y0ukn0wwh0/ConsoleGame/Console/console box/box model.PNG

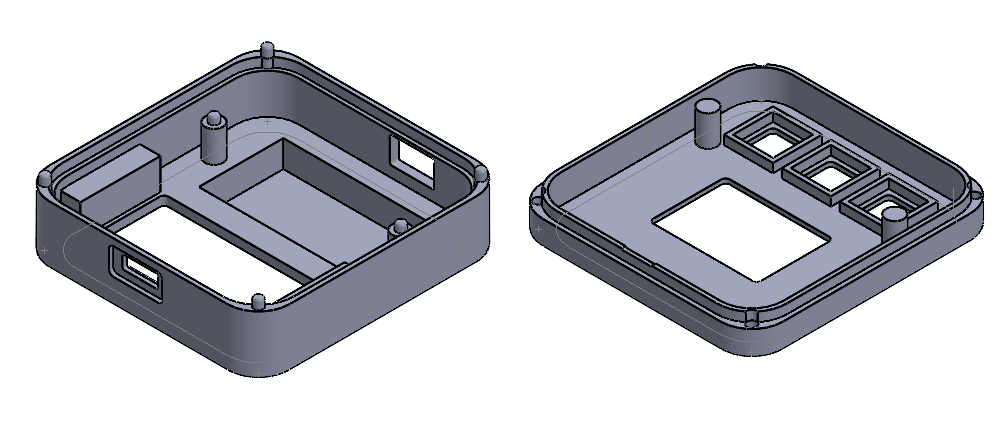
Console/console box/box model.PNG
