y0ukn0wwh0/ConsoleGame/Console/pcb.png

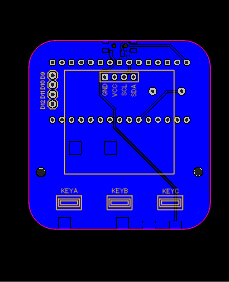
Console/pcb.png
