y0ukn0wwh0/ConsoleGame/images/feed.gif

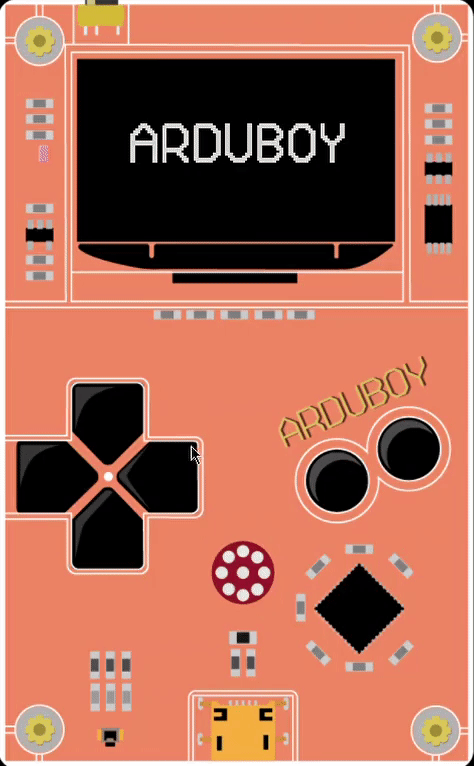
images/feed.gif
