y0ukn0wwh0/ConsoleGame/Showcase/box2.jpg

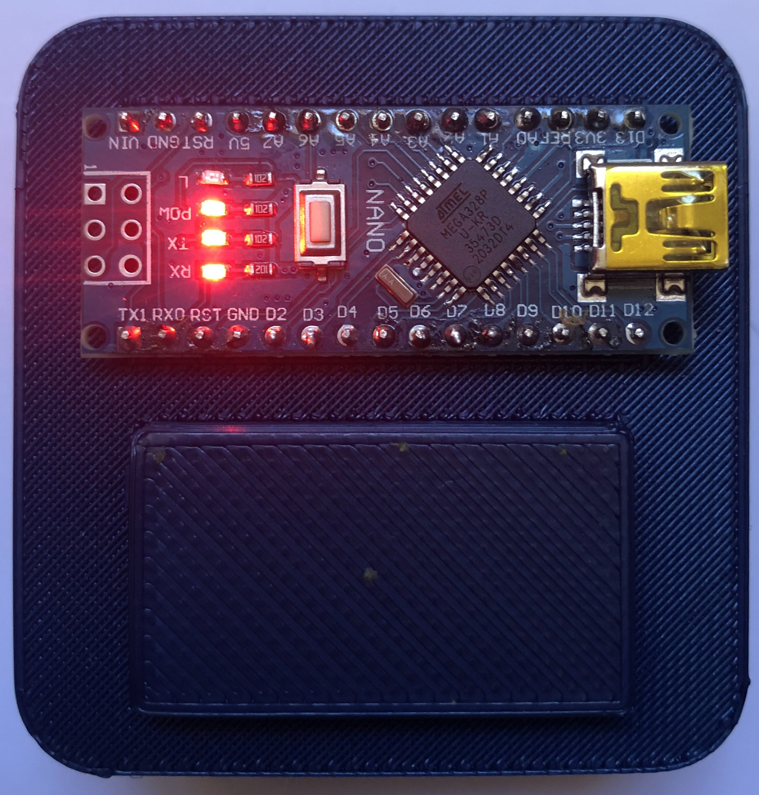
Showcase/box2.jpg
