y0ukn0wwh0/ConsoleGame/Showcase/box3.jpg

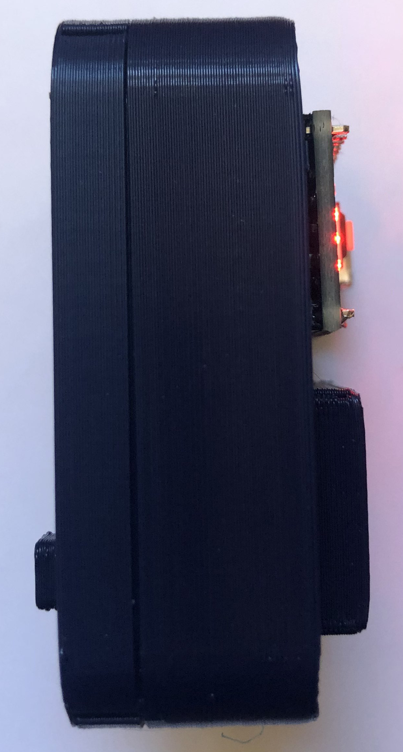
Showcase/box3.jpg
