y0ukn0wwh0/ConsoleGame/images/testComponents.gif

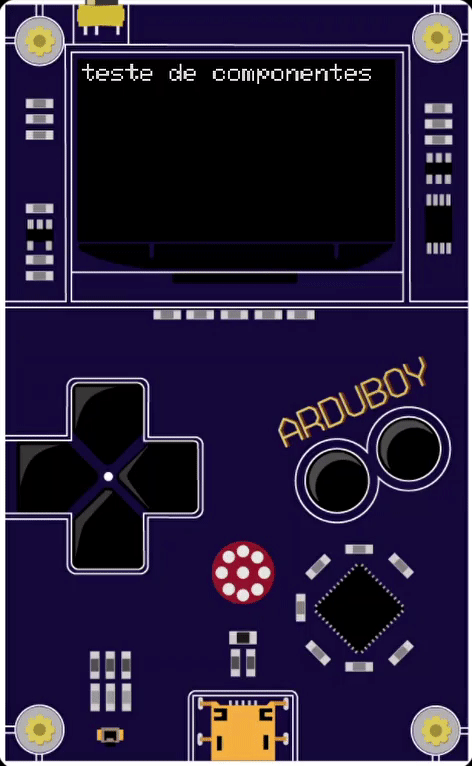
images/testComponents.gif
