y0ukn0wwh0/ConsoleGame/Game/game/sprites.c

#include <avr/pgmspace.h>

#ifndef SPRITES
#define SPRITES

//Game logo (73, 17)
const uint8_t PROGMEM logo[] = {
0x00, 0x00, 0xfc, 0xfc, 0xfc, 0xfc, 0xfc, 0x1c, 0x1c, 0x1c, 0xfc, 0xfc, 0xfc, 0xfc, 0xf8, 0x00, 0x00, 0x00, 0xfc, 0xfc, 0xfc, 0xfc, 0xfc, 0x00, 0x00, 0x00, 0xfc, 0xfc, 0xfc, 0xfc, 0xfc, 0x00, 0x00, 0x00, 0xfc, 0xfc, 0xfc, 0xfc, 0xfc, 0x1c, 0x1c, 0x1c, 0xfc, 0xfc, 0xfc, 0xfc, 0xf8, 0x00, 0x00, 0x00, 0xf8, 0xfc, 0xfc, 0xfc, 0xfc, 0x1c, 0x1c, 0x9c, 0x9c, 0x9c, 0x9c, 0x9c, 0x9c, 0x00, 0x00, 0x00, 0xfc, 0xfc, 0xfc, 0xfc, 0xfc, 0x00, 0x00, 
0x00, 0x00, 0x7f, 0x7f, 0x7f, 0x7f, 0x7f, 0x70, 0x70, 0x70, 0x7f, 0x7f, 0x7f, 0x7f, 0x3f, 0x00, 0x00, 0x00, 0x3f, 0x7f, 0x7f, 0x7f, 0x7f, 0x70, 0x70, 0x70, 0x7f, 0x7f, 0x7f, 0x7f, 0x3f, 0x00, 0x00, 0x00, 0x7f, 0x7f, 0x7f, 0x7f, 0x7f, 0x00, 0x00, 0x00, 0x7f, 0x7f, 0x7f, 0x7f, 0x7f, 0x00, 0x00, 0x00, 0x3f, 0x7f, 0x7f, 0x7f, 0x7f, 0x70, 0x70, 0x73, 0x7f, 0x7f, 0x7f, 0x7f, 0x7f, 0x00, 0x00, 0x00, 0x73, 0x73, 0x73, 0x73, 0x73, 0x00, 0x00, 
0x00, 0x00, 0x00, 0x00, 0x00, 0x00, 0x00, 0x00, 0x00, 0x00, 0x00, 0x00, 0x00, 0x00, 0x00, 0x00, 0x00, 0x00, 0x00, 0x00, 0x00, 0x00, 0x00, 0x00, 0x00, 0x00, 0x00, 0x00, 0x00, 0x00, 0x00, 0x00, 0x00, 0x00, 0x00, 0x00, 0x00, 0x00, 0x00, 0x00, 0x00, 0x00, 0x00, 0x00, 0x00, 0x00, 0x00, 0x00, 0x00, 0x00, 0x00, 0x00, 0x00, 0x00, 0x00, 0x00, 0x00, 0x00, 0x00, 0x00, 0x00, 0x00, 0x00, 0x00, 0x00, 0x00, 0x00, 0x00, 0x00, 0x00, 0x00, 0x00, 0x00, 
};

//Audio icon
const uint8_t PROGMEM audio[] = {
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
};

//Probability of the tier weapon being chosen (1-32)
//Example: if the random between 1-32 is bigger or equal to 16 the tier chosen is 1
//         if it is between 8 and 15 the chosen one is tier 2
const uint8_t PROGMEM tierProbs[] = {
  16, 8, 4, 2, 1
};
#endif
